curiouspl2/pic-lm75-thermometer/12f629_i2c_rs232_out_thermometer_routed_0.2_bottom.png

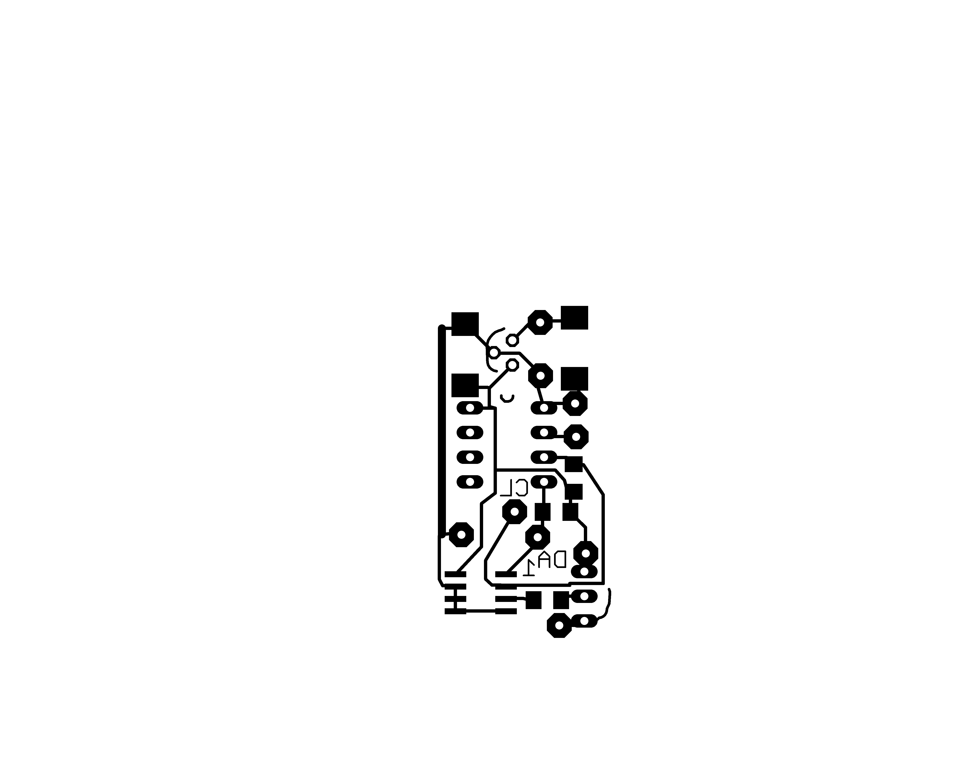
12f629_i2c_rs232_out_thermometer_routed_0.2_bottom.png
